Cisofe/MODULO-DE-CO2-PARA-CABINAS-TM-EN-BOGOTA/Diagramas/Caja Negra Módulo de CO2.drawio.png

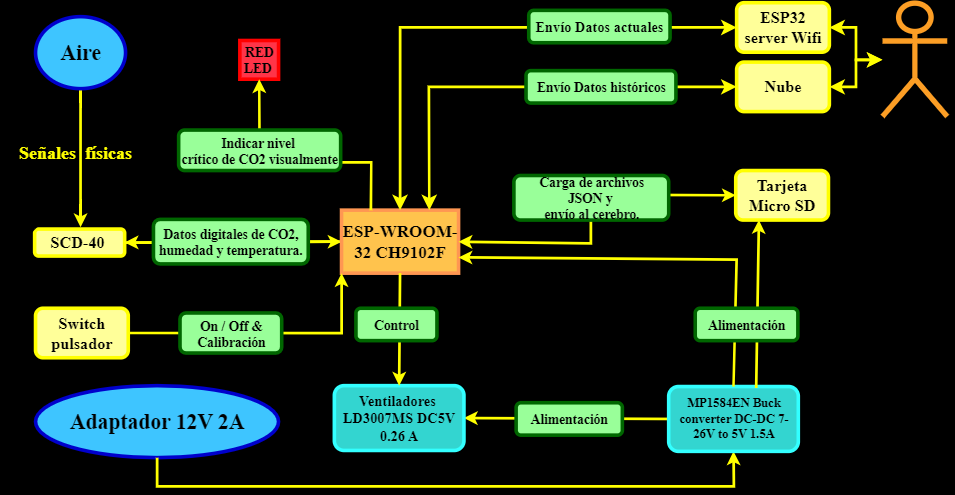
Diagramas/Caja Negra Módulo de CO2.drawio.png
