Cisofe/MODULO-DE-CO2-PARA-CABINAS-TM-EN-BOGOTA/Diagramas/Diagrama Tecnológico Módulo de CO2 para TM.drawio.png

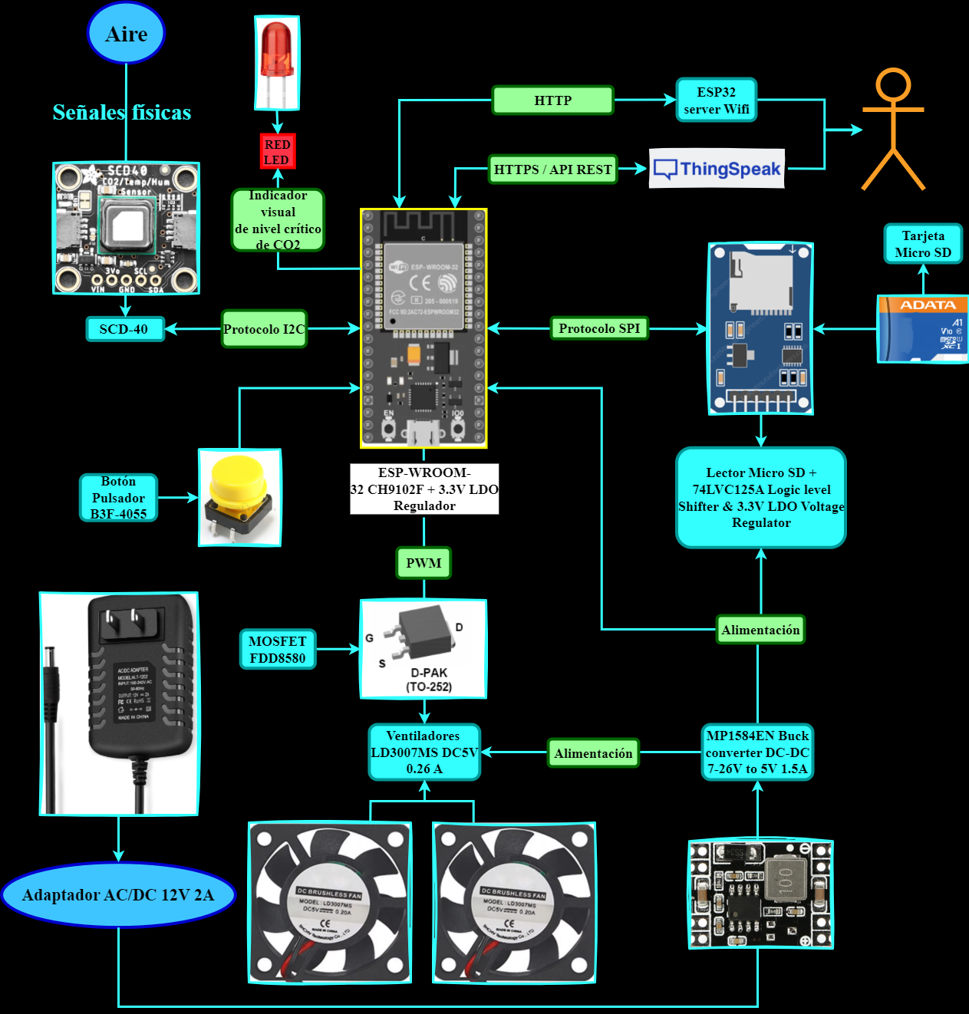
Diagramas/Diagrama Tecnológico Módulo de CO2 para TM.drawio.png
