Cisofe/MODULO-DE-CO2-PARA-CABINAS-TM-EN-BOGOTA/Evidencias/Evidencia_soldadura2.jpeg

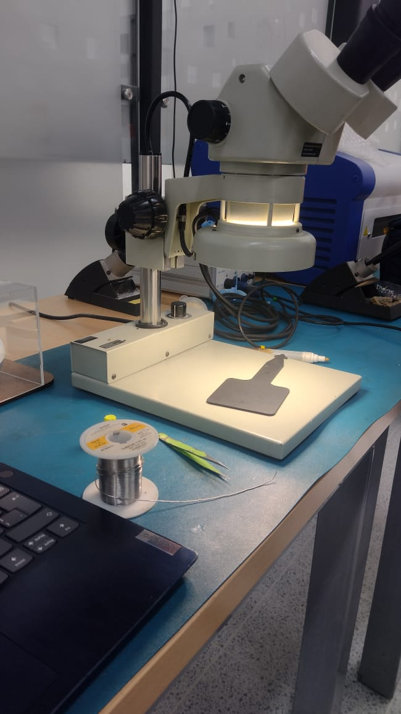
Evidencias/Evidencia_soldadura2.jpeg
