Cisofe/MODULO-DE-CO2-PARA-CABINAS-TM-EN-BOGOTA/Evidencias/Evidencia_soldadura_smd.jpeg

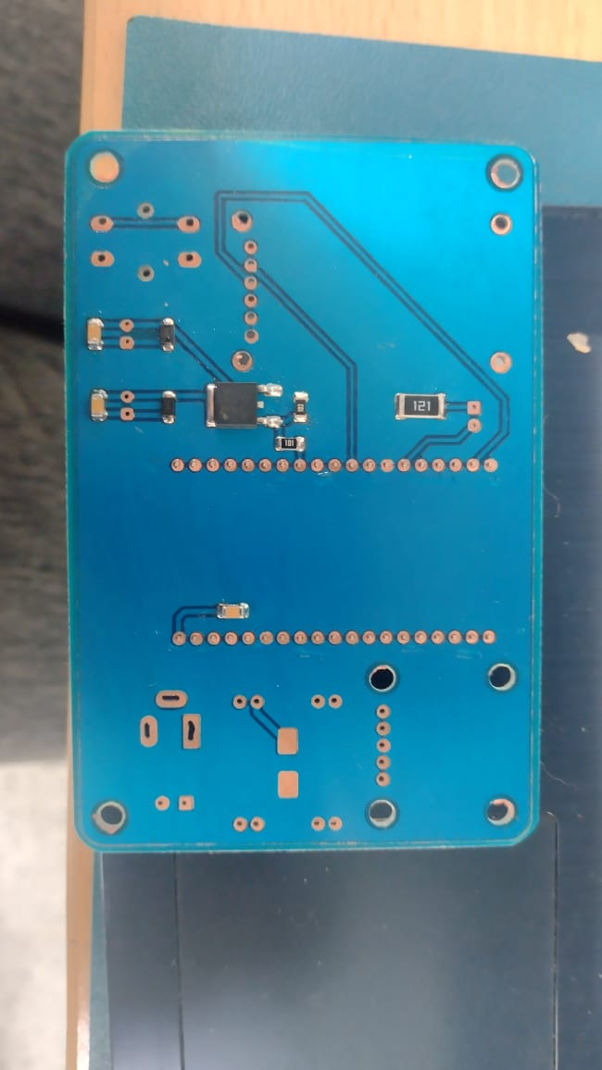
Evidencias/Evidencia_soldadura_smd.jpeg
