Cisofe/MODULO-DE-CO2-PARA-CABINAS-TM-EN-BOGOTA/Evidencias/PCB boceto.jpeg

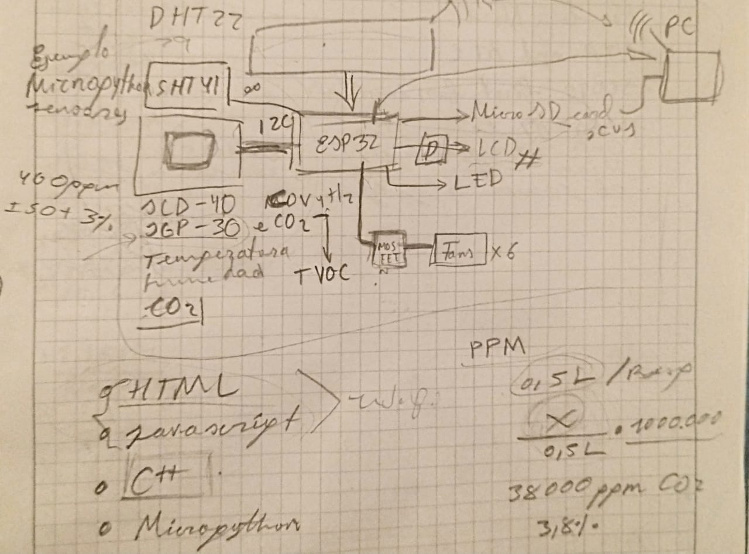
Evidencias/PCB boceto.jpeg
