Cisofe/MODULO-DE-CO2-PARA-CABINAS-TM-EN-BOGOTA/PCB/PCB-3D-Images/3D-Modulo CO2 de bus TM-Front.png

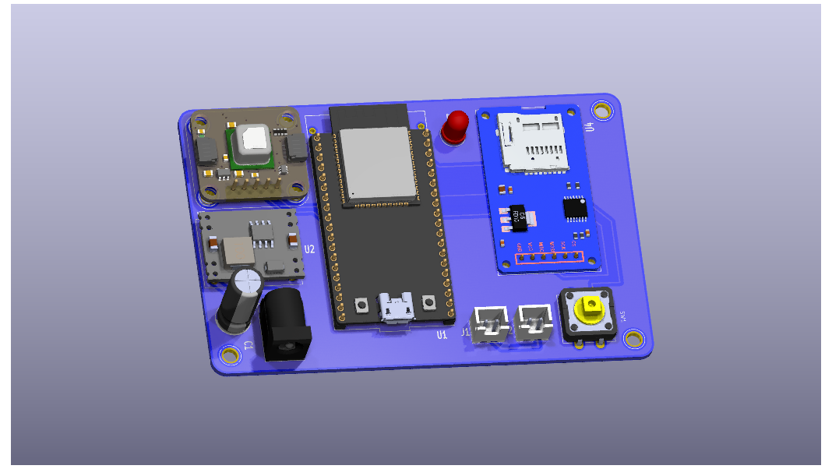
PCB/PCB-3D-Images/3D-Modulo CO2 de bus TM-Front.png
