Cisofe/MODULO-DE-CO2-PARA-CABINAS-TM-EN-BOGOTA/PCB/PCB_Front_Modulo_CO2_de_bus_TM.png

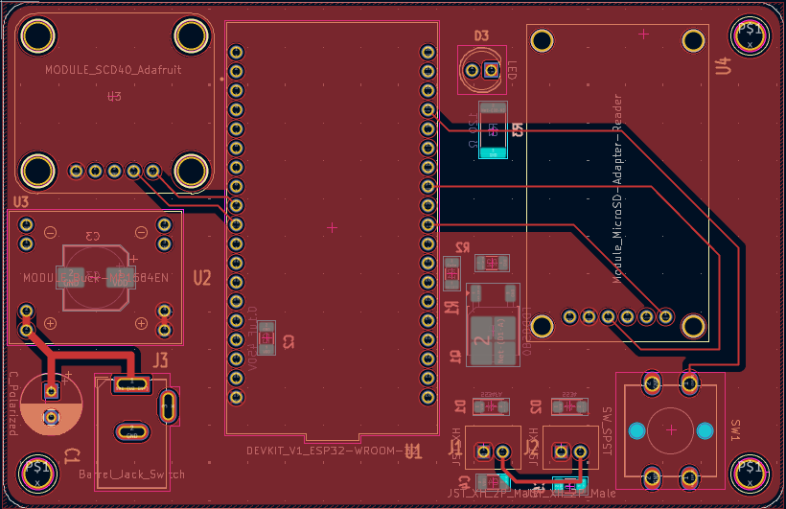
PCB/PCB_Front_Modulo_CO2_de_bus_TM.png
